Danjovic/ChessMate/firmware/uart.c

#include <avr/io.h>
#include "uart.h"


void USART0Init(void)
{
  // Set baud rate
   UBRR0H = (uint8_t)(UBRR_VALUE>>8);
   UBRR0L = (uint8_t)UBRR_VALUE;
   // Set frame format to 8 data bits, no parity, 1 stop bit
   UCSR0C |= (1<<UCSZ01)|(1<<UCSZ00);
   //enable transmission and reception
   UCSR0B |= (1<<RXEN0)|(1<<TXEN0);
   // Enable TX pin as output
   DDRD |= (1<<TXPIN);
}

int USART0SendByte(char u8Data, FILE *stream)
{
   if(u8Data == '\n')
   {
      USART0SendByte('\r', 0);
   }
   //wait while previous byte is completed
   while(!(UCSR0A&(1<<UDRE0))){};
   // Transmit data
   UDR0 = u8Data;
   return 0;
}

int USART0ReceiveByte(FILE *stream)
{
   uint8_t u8Data;
   // Wait for byte to be received
   while(!(UCSR0A&(1<<RXC0))){};
   u8Data=UDR0;
   //echo input data
//   USART0SendByte(u8Data,stream);
   // Return received data
   return u8Data;

}

uint8_t kbhit (void)
{
    if (UCSR0A&(1<<RXC0))
        return true;
    else
        return false;
}
